DigiTorus86/Teensy-R4ge-Pro/PlatformIO/teensy-r4ge-pro-shooter/include/wav_hihat.h

// Audio data converted from WAV file by wav2sketch

// Converted from hihat.wav, using 44100 Hz, u-law encoding
PROGMEM
const unsigned int wav_hihat[5953] = {
0x01005CB1,0x77766877,0xEAEC2195,0xE0737099,0x82807B70,0x88909012,0x8B822303,0x8C04180B,
0x090B9207,0x878EA413,0x1EB09F15,0x0B9B2122,0xA09E0094,0x51B2B980,0xD1485CCA,0xDACCBF48,
0xE8DFBB47,0xD7B254E2,0xA3E0DED2,0x56D9CDBB,0xBDBAE652,0x33ECEDE7,0xE9F8E450,0xE7C7605C,
0xC7C3C8E3,0x6264BED6,0x2B3ED7C3,0x736C5226,0x51535760,0x29C2DED8,0xD2E3E10D,0xE3E5BAA3,
0x0FC3D2D1,0xE2DFECC3,0x6744E3EE,0xF1E9B453,0x5CE53B58,0x3341465B,0xC03B5A56,0xB60A5293,
0xA4D1DACC,0xCEF0C15F,0xF0E59E5C,0x41C3D5ED,0xE7B56464,0xD2D25CC6,0xB54A5760,0x424C09E1,
0xB7C0D8DA,0xF5F46870,0x53BFCFC6,0x54C9E2CF,0x58BFD95A,0x65656556,0x50ECEA5E,0xD4E8F3D7,
0xD1535FBB,0xE4C937D0,0x626A5F4D,0x57716736,0x4C6B62D6,0x656949E5,0x615AD16B,0x673FF0D6,
0x056054D7,0x91E0E3EA,0xE5B8D4DD,0xD5E6456F,0xD52DCBDA,0x6425EDEE,0x628AC855,0xE487DEDA,
0x54DDD5C3,0xD6DECA48,0x4E23614B,0x5651D7C1,0x9DEBEB41,0xCEE8E4B7,0xE05262C0,0xA4A9D760,
0x34AE5FD0,0xE8BD44DF,0xF559C0F0,0xE5F43FE4,0xDF616357,0x29D1564D,0xC26D66D5,0xD7D6DCDE,
0xD9905433,0xD75E4FD8,0xC5C6D8E4,0x5E68AF42,0x546C18F2,0xE0E1D4D9,0xDBE3C22D,0x719ED751,
0x5561CE45,0x6E4E3C58,0x71755D65,0x66789DDC,0x6E61D5E5,0x68DA616C,0x685CC074,0x70E1CE51,
0x73535E73,0xE6E8E370,0x6FD46463,0x1E62F2C5,0xF4557BC9,0x78E28170,0xD851B867,0x6E656BA1,
0xE27107D4,0x79A85A20,0x70D5F46E,0xBFE4E060,0x645AC550,0xF1E7DC37,0xDC5177AF,0xD0E75465,
0xE05BA422,0x6F6864E2,0xF6F0E1A2,0x416966D7,0xC273D8F5,0x426366E1,0x63CDCF4C,0x54E33B74,
0x65706A54,0x66E0D363,0xF3D55361,0xDDF25920,0xF5266B69,0x44E243C5,0xD96A6362,0x7555E6F6,
0x57EFF7C4,0x54727377,0x661E5A40,0x2EB7C45C,0xE55B5A5D,0xD0CCB2E7,0xD953CAB0,0xE8E0735A,
0xD0637156,0x4829603F,0xC25F5148,0xE67055D7,0x5F5852EC,0xC7AC6D57,0x5859615C,0x4C626340,
0x7D65E342,0x7268446A,0xE01C7377,0x424B620E,0x6D5A3856,0x60E1FBE9,0xEDB5CFB2,0xD83063E2,
0x713CE954,0xDD7A764E,0x71E95E5C,0xF067777F,0x5E7252EC,0x707964E8,0x0D354230,0x68666269,
0x77D0D463,0x604DDF55,0x5ED8E657,0xB5EB5C77,0xF0E8BF3B,0x67685509,0x5E7754E0,0x46F2F2DC,
0x5A6E5C60,0xE35E6C0E,0xC4E16251,0xF7D8625F,0x72DFC0D3,0x67E4F45A,0xC2E0E9D6,0xDFA0616E,
0xCCF5E8C8,0x39665864,0xD3E562B4,0x6A5C4B51,0x5D57F045,0x3B7046E0,0xA22F53D2,0x6D6AEBE5,
0x507754E2,0x6A2B6C56,0x7537C470,0xA4D6707C,0x48E0EB53,0x597B6C25,0xD2936034,0x63B7B7C6,
0x493EA465,0x4F4EE0E0,0xE35851D4,0x5772F1FB,0x61D9F3F1,0xBAF2E462,0xECE3A25D,0xBB40DBE7,
0xCFE53FD2,0xE4D5D589,0xD0E941B7,0xBEECDA61,0xDA606F63,0x43206949,0xF8DD666B,0xD0DB5ADF,
0x6141DE47,0xE8F3E43B,0xE66767E5,0xD36D58C5,0x63A1E3F4,0x57E4E329,0xECD45259,0x3ED7B8C2,
0xB0D9D267,0xF1607463,0xD96169EF,0xC9DDC7B3,0xCB716385,0x5E6EE0F5,0xCE54D5ED,0xD5A15BC1,
0xF3D15755,0xB5DCB0F0,0x67572960,0xC0D6F8E7,0xE0482CD2,0x683548C3,0x6CCBD85C,0xE9EE5B70,
0xE39E665F,0xF1EC5C4C,0xD7DB41C4,0xE9694BE1,0xD9E4CBE7,0x706FD1E7,0xEBF8647A,0x69275766,
0xB531375C,0x7107DEA1,0xB133DB5B,0xF1FAECE7,0x45583842,0xF9F8E1C0,0x52E3625F,0x6662F0D1,
0xF1E3D3E0,0x771CE3D3,0xF4DBB073,0xD64C72E6,0xBC5FE5E3,0xCC48E4F6,0xDAE062B4,0x65E7E756,
0x64E6CC67,0x31F2E475,0x31B1E437,0x92319BE6,0x6B3DDFA1,0x52CB5465,0x449D7279,0x325F6160,
0xCFD96351,0x4A54DCC5,0x6D69D3DB,0xE4EFEDD5,0x6B56E6D1,0x454BEFEB,0xC4D5F2EE,0xD75631BB,
0xF2B75ADC,0xE8587595,0xE35356D7,0xF60561E8,0x26E0EBEB,0xB34FC5AD,0xD6DEEAEB,0xCE695ABD,
0xE0E0C0E2,0xC058735D,0xB9416149,0x5A5448C1,0xF0E26B70,0x195847D0,0x625BDAE8,0xE36963D3,
0x506962D9,0x64666459,0xC2C5DB27,0xE5BE53DA,0xD21EC03A,0x716AECF4,0x66E8E74D,0x6660D263,
0xEBEEFAEA,0xD5CC40D8,0xF4C740D0,0xD6E7B9E8,0xB5C1DF2D,0xD7AEE4EC,0xF1F3DED8,0xCBD0D316,
0x7463DBE5,0x764CEC4D,0xB05E5F68,0x5A65795F,0x6AECEF63,0xCDD2556E,0xDC246F66,0x276FC1EE,
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
};
