DigiTorus86/Teensy-R4ge-Pro/PlatformIO/teensy-r4ge-pro-gravitack/include/explosion_wav.h

// Audio data converted from audio file by wav2sketch_js
// Converted from XPLOSML2.wav, using 11025 Hz, 16 bit u-law encoding

PROGMEM
const unsigned int explosion_wav[3185] = {
0x030031bd,0x00000000,0x23008000,0x746f5b3e,0x6f707172,0x66686a6e,0x5d5f6064,0x97234652,
0xdfd4c8b6,0xebebe7e2,0xeeefefec,0xeceff0ef,0xe5e8eaec,0xd9dde1e3,0xd3d2d3d5,0xd0d0cfd1,
0xd2d0d2d1,0xe0ded9d9,0xe7e4e2e2,0xe5e5e6e5,0xe6e6e7e5,0xe5e7e6e6,0xe9e8e6e7,0xebedece9,
0xeaeaecea,0xe3e4e9eb,0x423623d6,0x32e3ede0,0x66655c5e,0x706e6d6b,0x71717170,0xac185166,
0xe0d8d2c4,0xeae8e6e1,0xebebeceb,0xe9ebebeb,0xe5e7e7e9,0xdce0e1e2,0xc6bac6d3,0xcbcfccd2,
0x983a17c2,0x60585751,0x70666663,0x71706b6f,0x6f6e6c6f,0x73727373,0x74727273,0x72737373,
0x71727273,0x6f707171,0x6064626a,0xc9185b59,0xb1acc8d0,0xd5d1b9ac,0xd3d3d0c4,0xd2d7d7d9,
0xdeddd9d5,0xdadddfdc,0xd8d7d7db,0xcdccd1d3,0xbdc9d1cf,0x1724acb6,0x230023b5,0x4245393a,
0x4a45434b,0x5e5e5f53,0x47484f5b,0x98364845,0xc5c0b6a4,0xd2c6c1c6,0xcccbd2d4,0xd7dad7d1,
0xd4d6dbd9,0xd5d2d1d4,0xd6d4d4d8,0xdbdbdad6,0xd3d8dada,0xd7d8dad5,0xdbdcd8d5,0xe7e1dddc,
0xf1f1ece9,0xf0f1f1f1,0xf3f3f2ef,0xf2f1f2f3,0xf1f1f1f1,0xf3f3f3f3,0xe7f2f3f4,0xebecefe3,
0xd0c7dcea,0xc8dadee0,0xb9c5cec1,0x5f534f44,0x6763615d,0x69696c6c,0x535b5c66,0x2c233a43,
0x2c402c17,0x43393635,0x3a17243d,0x2b41362b,0xc32c3597,0xc4c5c8c1,0x36b6c0c5,0x56544d42,
0x5e5b5b5a,0x595e5f5f,0x5955585a,0x57686961,0x5762624b,0x394d555c,0x80ab8136,0x39ac2432,
0x803e3945,0x554323ab,0x625c6160,0x6f6d6a6a,0x7472716f,0x6c707171,0x68686f70,0x65636467,
0x65616566,0x6b686a6e,0x6f6b676a,0x676a6e6e,0x6a6a6968,0x67656467,0x67676365,0x6c6a6b68,
0x6564646a,0x5a5c5c62,0x535a5f5d,0x50555957,0x412b4445,0x51525151,0x2b363650,0xb60080b5,
0xcdc8bec1,0xacabc5cc,0xc0ba9797,0xc3cbbdac,0xc7d9ddcd,0xc6cdcbcc,0x45483e80,0xe6c71831,
0xe7e9e8e9,0xebe6e3e9,0xece9ebeb,0xf1f0efef,0xf2f2f3f4,0xf3f2f1f0,0xedeeeff0,0xebecebee,
0xefedeeee,0xe7eaeeef,0xe6e7e6e6,0xabcbe1e4,0x5a534198,0x5e5f615f,0x5b606261,0x5f5d5b5b,
0x5a5f6160,0x41424752,0x4e474241,0x31003d52,0x4e4b544d,0xcd31514f,0x3d4744ab,0x40414a4d,
0x353a3932,0x3d504000,0xcbccb297,0xd9d7d4c6,0xdad9deda,0xe5e3dbda,0xb1d7e2e7,0xbdbdac3e,
0xdddbc2b2,0xb2d5d9dc,0xd7d2dccb,0xe1e1d0be,0xb1c9ccdd,0xc0beb5b6,0xdcd5ccbe,0xd8d7d8d6,
0xd6d8ccd3,0x645300c5,0x696b6865,0x72716d6a,0x6f707373,0x70717070,0x6f6e6e6f,0x70747370,
0x69727271,0x525f6463,0x31413d36,0x35363143,0xbab11736,0xe2dad3ce,0xe1e4e6e6,0xe8e6e5e1,
0xe0e7e5e6,0xacc6cfd1,0xb2b5b2b1,0x24312417,0x3118ac97,0x5f438024,0x65625d5f,0x706d6867,
0x72717070,0x71737472,0x73727272,0x616f7171,0x404d5759,0xe3decfb9,0xeae7e6e2,0xe8e7e4e7,
0xebebe5e4,0xeeefedec,0xd7e6ebee,0x24a4b1ac,0x49434032,0x59524d4a,0x54576261,0x98514e5a,
0xc0dbdfe0,0x53422c2b,0x45515759,0xb224353a,0x665b5445,0x63595261,0x52505f65,0x0043393a,
0xc93600ac,0xe9e4e0d4,0xf1f1efee,0xeae9ebf1,0xe2e0e5ea,0xf0eae8e6,0xd1d7d8e7,0xc5c2bac0,
0xcdbdd6d7,0xe9e6e8e4,0xe1e7eceb,0xe4e2e4e3,0xd9e2e7e5,0x2b0023ca,0x455842a3,0x5d53514c,
0x6e686765,0x4150606b,0xc5cac198,0xd6cfd2d0,0xdae0e6e0,0xe8e6e3e1,0xf2f3f2ed,0xeeeff0f1,
0xf1f1ebed,0xe3e9eceb,0x40c2d2dd,0x5b5a5d54,0x5c626263,0x4a47535b,0x41364e45,0x3d3a3949,
0x61615750,0x67676360,0x5b616766,0x4339515a,0x68656256,0x6d6b6a6c,0x6f6e6b6a,0x6767666d,
0x5a63605f,0x67595652,0x696b676a,0x364e656d,0xd9dcd9cb,0xeae3e2dd,0xf1f1eae7,0xf0eff1f3,
0xf4f3edf0,0xf0f0f2f2,0xe5edf1f1,0xcdd3d7dd,0xc8d4d5d2,0x31c2cfcb,0x3e3d4051,0x67635440,
0x665f6466,0x68686768,0x69706867,0x5f5e6465,0x64686259,0x635b5760,0x62646768,0x5861635d,
0x5d4b485a,0x6466635c,0x68636268,0x4d5b6061,0x53594b31,0x463a3239,0xd7dac749,0xedebece2,
0xcbe0e6eb,0xecede9d7,0xecebedef,0xebedf1ee,0xf3f3f2ef,0xebeef0f2,0xf1f3f0ec,0xe1e1e9eb,
0x98d0d3de,0x62616150,0x6b686566,0x6f6d6967,0x6e706e70,0x70706d6c,0xb5445162,0xc4d2cccd,
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
};
