DigiTorus86/Teensy-R4ge-Pro/PlatformIO/teensy-r4ge-pro-gravitack/include/fire_wav.h

// Audio data converted from audio file by wav2sketch_js
// Converted from Fire1.wav, using 11025 Hz, 16 bit u-law encoding

PROGMEM
const unsigned int fire_wav[1185] = {
0x03001270,0x00000000,0x00980000,0x0000ac18,0x181836b2,0x364f4f4f,0xdad1d0d0,0xb6d3cdcb,
0x3a24c3be,0xb6625598,0x364551ac,0x543a6267,0x4d606c41,0x00980055,0x00984b64,0x4fbed4cf,
0xe8e3e1c1,0xdfbedae4,0xdfe8e7f0,0xe2d34bd2,0xc9bae1e2,0xe3cbdc45,0x60514bd5,0x005d65c3,
0x3e636f51,0x2c6d595d,0x55536041,0x6f666324,0x4361586b,0x71635959,0x5c64615d,0x416e6950,
0x24d1cfa4,0xc5ace1d4,0xd8e3e5d0,0xe6e400cf,0xeaf0f4f2,0xdae7e4e5,0xe6d4e1d9,0xe6e6d2a4,
0x2ce0e6ef,0xb2cd455d,0x6951002c,0x45322465,0x3ab26153,0x5c685f65,0x6d5d5443,0x566a6969,
0x5a575247,0x98d49862,0x61566059,0x41ba555f,0xdacddda4,0xb200dae2,0x4fa4c7b6,0xec41664f,
0xe0ebefef,0xbeacd8db,0x4b534fb6,0xcde1eee6,0xe9e0e5da,0x473e43de,0x98b6005a,0xdcd4acba,
0x5c98d1cf,0x5498a449,0xd2595552,0xba3eb2e1,0x6c43a498,0xc14f3a67,0xc94b47c7,0x625551c1,
0x5c003654,0x53604b5a,0xcb3a2400,0x4f5745d5,0x564f5866,0x50acd8c9,0xa4d1dbc3,0xbab22c3a,
0x50505256,0x2cd15064,0x4dc598cd,0x6372624b,0xb6495151,0x324be200,0x655f6f61,0x00d651c5,
0xba36c718,0xd851c132,0xcface0d7,0xb22453d0,0xd4d618e1,0xe2c7e2e1,0xc9e14d00,0xe6ecdfd7,
0xe6b6e9d5,0xd098e3c9,0x47e2cbe0,0x630052d9,0xd3be3ea4,0xf14fd44f,0x5547e251,0x60e658e0,
0x545555e0,0x246d366b,0x58514d69,0x66be6ac3,0xc1735361,0x57433e61,0x49ba60d5,0xd84fb6ac,
0xd1e0b6d0,0xd6b698e1,0xe249f041,0x45f098d3,0xe118d6e6,0x543eba43,0xc936acd5,0x58d56000,
0x415e52c9,0x4f65d573,0x43d34300,0x4d3a9850,0x43d956c1,0x00e0c3c5,0xed66ebc3,0x5cde4763,
0xa4cf57e5,0x00dcac47,0xcf6ad5ba,0x6d005f60,0x515a5849,0x3a6bc961,0x74eb695a,0xd6632c3e,
0x435b435f,0x6350525c,0xdc183eba,0x50e2a436,0xe55dd0e6,0x4fd5d064,0xdacd63e7,0xd1c3ea56,
0x45d7cdd1,0xede0b6f1,0xb2dff055,0xe098d9ed,0xd7d24dc7,0x5de5d332,0xe651ebe0,0xcbddd5e1,
0xd5d436cf,0x4be0cf4f,0xd251d2cb,0x55ba53ac,0x005ae018,0xba475cd0,0x5c36655c,0x603a4d69,
0x5e5d1850,0xa46755c5,0x5e476a5e,0x6b65636f,0x6bb25b68,0x6660dd63,0xe17154e3,0xd2d367be,
0x2cacc94f,0xea4552e3,0x3ae55251,0x6dc3e662,0xb260d0cf,0xd70054d7,0xcfd5d7ac,0xe1bad6e3,
0xd0c9c1d9,0xeb4f00e6,0xf0df61dd,0x36f4005f,0x45c5e855,0x9847d5dc,0xd4ba3ecb,0x18d0ba00,
0x5618d6cb,0x323ac198,0x592cb247,0x6543c54f,0x645ad798,0x325f43c3,0x32b6534d,0x52c9a45c,
0x6251cf51,0x52544f49,0xc1c94b4d,0x55ba9845,0x5f2cd436,0x4f4bb654,0x6455ac45,0x5862544f,
0x006a63ba,0x186c6b18,0x186a6341,0x4b7163da,0xc95d00e1,0x3a5cd1ee,0xc34dc9d9,0xd5e0e0c9,
0xcfeee3d7,0x36e1f0d8,0x56bae1c3,0x6863d8d6,0x6353e000,0x6845e5c5,0xb2e6e400,0xdeece000,
0xe4f3c558,0xe8ead636,0xc1dfc7d4,0xcdb6d2a4,0x5bd4e1c3,0x55e3e5c7,0x52d1de52,0x5a00c95f,
0xd7cb9853,0xd1dab600,0x4500d3e8,0xcb51d8de,0x323ae0c1,0x5acdac00,0xc14b622c,0xb2625f3e,
0x2447c798,0x47c14b58,0xc5496b56,0x5956513a,0x61521818,0x62724d50,0x74646264,0x68596063,
0x5150646c,0x2c592465,0x32d94947,0x5224cfba,0xa4d1c9cb,0x4936d03e,0x4300d600,0x0098b63e,
0x5d3e5c18,0x4bba3653,0xc14b646a,0x554d6366,0x2c607064,0x41455949,0x415745b6,0xbad6c924,
0xd2a4c500,0xd5d1e1e5,0x24dae4d9,0xd8ac453a,0x2ccfdcd8,0xc1d93ec3,0xebd2d041,0xe3d1cfd6,
0xd7d7a4e4,0xdcdddedd,0xe9dfe4e1,0xe1dce6ee,0xe3e3e1db,0xe1ead7e5,0xf4beeae8,0xc5e0e5f0,
0xd8e4e3e8,0x3ac5d1c1,0x5b4bb618,0x2c415964,0x5a59695c,0x4b5b5058,0x5d626152,0x51582c2c,
0x53cb4b50,0x2c59535f,0x56605b49,0x576098b2,0x98c54943,0x54c9dcc7,0xe7ddb25f,0x18b232d7,
0xd800dcd4,0x645258cd,0xd4c1d441,0xd4c94d57,0xb64351df,0x2c476060,0x4b6051b6,0x60410053,
0x5bd2495e,0x3265666c,0x6a6663c1,0x4b41d25c,0x45596963,0x5f36183e,0x4b675149,0x53d3d1ba,
0xe0cb4b56,0xcdba4d32,0x605bd4de,0x5a3ecf47,0x414d6452,0x4f676056,0x6566acba,0xcfcf4300,
0xd7be625c,0x545eb6be,0x4163bae4,0xc9e84d61,0x63684947,0x005955be,0x4dd0364d,0x3e662c55,
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
};
