DigiTorus86/Teensy-R4ge-Pro/PlatformIO/teensy-r4ge-pro-gravitack/include/refuel_wav.h

// Audio data converted from audio file by wav2sketch_js
// Converted from Jump1.wav, using 11025 Hz, 16 bit u-law encoding

PROGMEM
const unsigned int refuel_wav[3553] = {
0x0300376d,0x00000000,0x00000000,0x00000000,0x00000000,0x00000000,0x00000000,0x00000000,
0x00000000,0x00000000,0x00000000,0x00000000,0x00000000,0x18180000,0x24180000,0x2c323224,
0x182c322c,0x32362c24,0x2c2c2c36,0x24001818,0x323a322c,0x36363618,0x41453e3e,0x323a4141,
0x3a3a3232,0x43433a36,0x41364345,0x453a4543,0x434b4143,0x24364747,0x3a323a3e,0x3a435151,
0x49494736,0x41415151,0x00002c32,0x4149413e,0x3243363e,0x24182c00,0x182c3636,0x98323e00,
0x18243200,0x3a3a1818,0x0098ac24,0x24324341,0xc1ac0000,0x2c00acc7,0xd0cfc398,0xb2b2c1c1,
0xcbb200b2,0xc5c9c5cf,0xacc1c3c1,0xc1c1c7b2,0xb6c3b2c1,0xb2000098,0xc3c9c7c5,0xc3acbab2,
0xcdcbc5c1,0xc7c7c1c9,0xc198bacd,0xcdc7bac1,0x00c1cbc7,0xc5c9b200,0x18acbac7,0xa42c003a,
0x36acb6a4,0x32364941,0xc5ba1800,0x323eacac,0x24a42c41,0x98a4412c,0x002c323a,0x00003a32,
0x2c36acb6,0x41414747,0x36413a2c,0x433a4336,0x243a3a45,0x1800a400,0x3a18ac98,0xb6ac2c41,
0x433a2498,0xa4b22c36,0x36a4b22c,0x2c322c3e,0xa432433a,0x324543a4,0xa4a44143,0x189824a4,
0x004b4541,0xc3b6a498,0x410036b2,0xbeba0041,0x182c98be,0x1845433a,0x2cac9800,0x18003618,
0x243a3a24,0xba98a498,0x413a3649,0x00b64136,0x45430032,0xbebe3e41,0x3e000000,0x00494749,
0xb6ba18a4,0x983a3ea4,0xa4ba0024,0x3600a418,0xb2182c24,0xcbb6c5c9,0x98ac24a4,0xc7b224ba,
0x3200c3be,0x0000003a,0xbabe98c7,0xb22c00ac,0xb2b2b6c1,0xbe00c5a4,0xa4beacba,0xaccbc7be,
0xbebabac1,0xcbb6cdc3,0xc3d0c5cf,0x3232ac3a,0x00d3cfc5,0xa449cbcd,0xcdcd47a4,0x4b51982c,
0x32be363e,0x43a4c143,0xc343accf,0x514398ac,0xd24345c5,0x3eba0049,0xd7b22cac,0x49cb98b2,
0x414f184d,0x36005198,0x59492c61,0xac514d32,0x53a44736,0x4345244d,0xc5495600,0x3a2c5358,
0x3641c13a,0xbe434fcd,0x52005449,0x2c4dc724,0xac494fbe,0x3a32364f,0x532cb64b,0x322c4bb2,
0xd13647ac,0x4d243258,0x2c98d4d2,0xc54db6cf,0xcde22c00,0xa400d618,0x98be00cd,0xdb2cd0d5,
0xb2d64ba4,0x32bad445,0xacbe98c9,0xc32cba24,0xd9c124d8,0x003ac724,0xc5d32cd2,0xd0c7c3b6,
0x00c92c36,0xd0becfc1,0x4500be2c,0x18c718ac,0x3298d1c5,0xac3a0051,0x43d498a4,0x432c3e45,
0xd424b62c,0x18ac3a18,0x2c2424b2,0x002c4b32,0xac472c98,0x0041493a,0x4345c9b6,0x51415200,
0x4f45b6ac,0x244f3251,0x5445362c,0x2445412c,0x2441aca4,0x364147a4,0xc932c7c1,0xcbba5b24,
0xbea4c100,0x49cb4341,0x3636c14b,0x184941c1,0xc345c7be,0x98c74dcf,0xbe00984f,0x18d31898,
0xb250b232,0x41240032,0x2c434dd3,0xcb364147,0x00c9514b,0x49004153,0x4b49c92c,0x432cac24,
0x005145c7,0xd1004fc1,0x4f24b656,0x00cb5459,0x4dbab2b2,0x523e4353,0xbe3ed100,0xac5041b2,
0xcda45918,0x00c32ca4,0xc3cb414d,0xc1d8cd32,0x49becb3a,0x36b2cd24,0x3ed2dabe,0xa43ed0cd,
0xdba4acd4,0xd500b6db,0xdac3b2d3,0xe0e000a4,0x18dababa,0x32d2d636,0x3eacd9b2,0xc1b2d3cf,
0xc3c9d2d6,0x00bacdac,0x50c3d1c3,0x0032d1c7,0xc759acd2,0xb24f55c3,0x00c35436,0x3ed10058,
0x5800b655,0x4947d400,0xba574dc1,0xcb2452ba,0x3ed15150,0x4743c147,0x4152524b,0x4b555318,
0x5a43495d,0x5951474f,0xbe593a98,0xb64b622c,0x4b3e554b,0x554b0058,0x002c3632,0x5000433e,
0x6257004d,0xc155beb2,0x003656ba,0x3649a441,0xc9243ecf,0x36c72424,0x00181845,0x98d3a43e,
0x43b2d03e,0xd2d5c9c9,0x00cbe000,0xd1c7c3dc,0x18b6d5c9,0xd6cdc3d9,0xd63ec5c3,0xc5e0acc3,
0xa4c5acbe,0xc7cfcb49,0x5041d1cf,0xd3a4b2cf,0xc7baa4d1,0x00c7b22c,0x45a4cf3a,0xa449bec7,
0xa44d53c1,0x98cd4d41,0x4b00d03a,0x1853acac,0xbe4151cb,0x56325057,0x4549ac55,0xa45041d1,
0x45b24f41,0x324d0043,0xcf4b50c3,0x52ac2c47,0x3e36c52c,0x24ac36b6,0x524b9853,0x001898be,
0x50451898,0xd7a445a4,0x98c9b64d,0x003a00b6,0xbed5d1c7,0xba43b2d0,0xc3c7c9b6,0x980036d0,
0xac32b641,0x47324f00,0xac2cd2ac,0x983ab6b2,0x98c718cf,0xacb2bac7,0x2c49c941,0xaca41898,
0x5400543a,0x0098ac4b,0x3245bac7,0xba45182c,0xac003a32,0x49004324,0x18434118,0xb6494932,
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
};
