DigiTorus86/Teensy-R4ge-Pro/PlatformIO/teensy-r4ge-pro-gravitack/include/warp_wav.h

// Audio data converted from audio file by wav2sketch_js
// Converted from warp1.wav, using 22050 Hz, 16 bit u-law encoding

PROGMEM
const unsigned int warp_wav[5825] = {
0x02005aec,0xa6a6a7a5,0xa8a6a7a7,0xaaaaabab,0xacaaabac,0xadadaeae,0xadadb0af,0xb0b0b0b0,
0xb1b1b2b1,0xb2b2b3b2,0xb2b3b3b3,0xb3b2b3b3,0xb4b4b4b4,0xb5b6b6b6,0xb5b6b8b7,0xb7b7b8b6,
0xb6b7b8b7,0xb9babab8,0xb9b9b9b9,0xb9babab9,0xb9bab9b9,0xbbbbbab9,0xbabababa,0xbbbbb9b9,
0xbabab9b9,0xbabab8b8,0xbbbab9b9,0xbbbab9b9,0xbbbbb9ba,0xbbbbbab9,0xbbbbb9b8,0xbabbb8b8,
0xb9b9b7b7,0xb8b8b6b7,0xb6b6b6b6,0xb5b7b5b5,0xb5b6b5b4,0xb4b6b5b4,0xb3b5b5b3,0xb2b4b3b2,
0xb0b2b2b1,0xb0b1b1b0,0xaeb0afae,0xadb0aeac,0xabadacab,0xabadaaa9,0xa8a9a8a8,0xa8a9a7a7,
0xa7a7a4a5,0xa4a4a2a3,0xa3a3a2a3,0xa0a1a1a1,0x9e9e9a9a,0x93979797,0x90908888,0x8a8e8783,
0x00898783,0x07878403,0x0d80030c,0x150a0a10,0x190c0b15,0x20161619,0x211b1b20,0x221d1b21,
0x231f1d22,0x23201c21,0x24221d21,0x27262223,0x29262123,0x28282527,0x29282525,0x29292424,
0x2a2a2624,0x2b2a2525,0x2c2c2826,0x2b2b2929,0x2b2d2c2b,0x30302c2a,0x30302d2d,0x31312f2e,
0x31313030,0x31302f30,0x31313131,0x31303031,0x322f2f31,0x32313233,0x31303032,0x312e2d31,
0x302d2f31,0x302c2d30,0x2f2b2b30,0x2f2a2a2f,0x2d2a2a2f,0x2d29292b,0x2d29282c,0x2c29292c,
0x2a28262a,0x2825252a,0x26252628,0x25242527,0x20202224,0x1f1f2021,0x1c1b2020,0x1d1c2020,
0x171b2121,0x13131b1b,0x0e111918,0x09091313,0x09081413,0x06051212,0x05041110,0x81800b0b,
0x85880206,0x06070c0d,0x03030f10,0x0a060602,0x02020c10,0x0f0d0702,0x06030309,0x8b898601,
0x86878f8e,0x85858d8d,0x84818a8e,0x80048889,0x8f8a8f8e,0x87888f92,0x8402858b,0x8b01828b,
0x83869091,0x8b818183,0x9188898e,0x8a888d91,0x8e909090,0x888c8c8c,0x8a8a8482,0x9094918a,
0x9c9f958a,0x9c9c9291,0x9ca09c99,0x92999494,0x999d9186,0x85928e8e,0x8b968f03,0x94948308,
0x949a9691,0x8f97948b,0x8596958a,0x90958a08,0x90969183,0x919b9889,0x848f8905,0x8e938706,
0x8e928880,0x8d97948a,0x8f918702,0x999b988f,0x9da09a94,0x99a09e98,0x95999390,0x8e939290,
0x93958d83,0x8287878a,0x868e8800,0x07030303,0x8b86070e,0x85000086,0x86008085,0x83030287,
0x83070189,0x8b00888e,0x88058691,0x0e160c8b,0x15180c00,0x00120f0a,0x89028690,0x860c8192,
0x85088f95,0x84019193,0x0312078e,0x00078f94,0x0c140a85,0x04130a83,0x181c1480,0x131a140e,
0x890f1006,0x0706929a,0x19190588,0x16160909,0x08181814,0x01089091,0x01849595,0x09130c02,
0x100f8790,0x10160803,0x11118383,0x191f1911,0x23231a12,0x151c1c1c,0x191d1109,0x141d1513,
0x03038585,0x82028383,0x11100187,0x1c201911,0x1b1d1715,0x1c1c1715,0x1f1f1a17,0x191d1c1c,
0x8f89820b,0x94949292,0x95939494,0x90919597,0x81858e90,0x1e181105,0x1c1f1f1f,0x030b1217,
0x8e878081,0x04008890,0x01020104,0x0a0f110b,0x1a1d1a11,0x0e141616,0x8e820908,0x99928f8f,
0x9d959599,0xa19c9b9d,0xa7a3a1a1,0xa6a6a6a7,0xa6a5a5a6,0xa4a3a2a4,0x8c969ba1,0x1916160c,
0x191a2020,0x988f0d18,0xa2a29b98,0x9fa19d9d,0x97999797,0x150f0187,0x92920d18,0x10859293,
0x0a0a171a,0x2216120f,0x24252626,0x23252626,0x91910019,0x11018b8b,0x160b0f14,0x181f201e,
0x96968d0d,0x99999696,0x04919999,0x8186050b,0x1a120c0c,0x0102131c,0x12050306,0x211e1f1f,
0x23242726,0x0b111a22,0x9996870b,0xa3a5a099,0x1590989e,0x28232623,0x2223292c,0x928b1421,
0xa0a19990,0x939d9a9a,0x10828288,0x048c0818,0x1d0e1216,0x26232324,0x07142128,0xa3a29785,
0xa9afaaa3,0xa2a6a5a4,0x9ca09e99,0x959e9a94,0x8f9e9a90,0x96958a08,0xa4a39b97,0xaeb1ada6,
0xa8acabaa,0x96a2a3a5,0x21140a87,0x171d2224,0x89810c14,0x91949290,0x98969491,0x04859197,
0x17150d08,0x1f191313,0x121e2021,0x95929183,0xaaa4a29d,0xa3a5aaad,0xa6a3a3a3,0xada9a9a9,
0xadaeb0b0,0x020e95a7,0x9f988f87,0x821380a0,0x9ea1a4a0,0x2b291c91,0x2e2f2b29,0x16272b2b,
0x939ba19a,0x07180d8b,0x211f128c,0x9e07121a,0xa9a5a9aa,0xa0a5abae,0x17251693,0x09899784,
0x80171106,0x1185999a,0x2c332b1b,0x23252224,0x2224201c,0x33322b20,0x27323131,0x8c15181b,
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
};
