DigiTorus86/Teensy-R4ge-Pro/PlatformIO/teensy-r4ge-pro-tombstone/include/explosion_wav.h

// Audio data converted from audio file by wav2sketch_js
// Converted from explode_11k.wav, using 11025 Hz, 16 bit u-law encoding

PROGMEM
const unsigned int explosion_wav[2809] = {
0x03002bc3,0x80008000,0x80008000,0x80008000,0x80008000,0x80008000,0x00000080,0x00800080,
0x00000080,0x00800000,0x80808080,0x00800000,0x00808080,0x01800080,0x01800080,0x01800180,
0x01800281,0x02810182,0x80000000,0x83018000,0x85068404,0x88098609,0x89098909,0x86078908,
0x05818304,0x53545183,0x55535453,0x8a129f48,0x0b850301,0x55511a8c,0x044e5552,0x08880b83,
0x03880689,0x870d8380,0x53545225,0x008d4c55,0x5546a01c,0x32545353,0x8498079b,0x8f828a8e,
0x85988597,0x5255499d,0xa92a5254,0x5439a025,0x44565254,0x988a949c,0x5453554c,0x54545353,
0x01914e56,0x94910f01,0x4e0b818b,0x53555356,0x52545355,0x53535353,0x53535254,0x92315453,
0x06168b03,0x3fa01d87,0x53545355,0x53535353,0x53535352,0x54545453,0x53535454,0x38545353,
0x1fa11f9d,0x56515551,0x1998064c,0x5355459f,0x9b335353,0x83049609,0x99870305,0xa1039991,
0x55515549,0x1ca53153,0x545231aa,0x95465753,0x01909b13,0x96058889,0x8a140982,0x1b961004,
0x535545a1,0x53535454,0x53525353,0x54545453,0x54535453,0x54555454,0x13993454,0x8804808c,
0x56419114,0x53535453,0x54545453,0x54555454,0x53545354,0x05924555,0x89901492,0x16010099,
0x3a9e1a91,0x55535354,0x95209742,0x8f8a0617,0x8080920e,0x818d0c92,0x48a00f83,0x52555356,
0xa724a033,0x53545235,0x82a34656,0x11110c94,0x00948594,0x369d1496,0x55535454,0x8e019543,
0x09998507,0x5453299d,0x54545454,0x40555353,0x169a1da7,0x06861482,0x1b811496,0x53554098,
0x54545455,0x54535354,0x54535454,0x55525453,0x04169344,0x889b9685,0x54522197,0x53535453,
0x42555353,0x18a01ca1,0x5552554e,0x229b1150,0x535440a3,0xa03e5552,0x86908d02,0x31a31388,
0x55525452,0x940da146,0x84818910,0x92118c92,0x54389504,0x43545353,0x1581169c,0x5552554d,
0x1b932350,0x53543ca7,0x54535354,0x54545453,0x54535453,0x54545453,0x53535454,0x189b3e55,
0x5450189b,0x53535453,0x45555353,0x87921199,0x87089203,0x53545223,0x53545455,0x53535353,
0x53545454,0x54545353,0x53535354,0x53545453,0x169f4056,0x87878697,0x53329b15,0x46555355,
0x0a80149f,0x02061112,0x1a848f04,0x53543699,0xa0445453,0x4e0a910e,0x51555355,0x8a84841c,
0x01809184,0x08878186,0x54501112,0x0d4f5552,0x41a41995,0x55545455,0x8f19a23f,0x53555118,
0x54535353,0x94455553,0x8015881d,0x24100c85,0x53535452,0x54535452,0x55535553,0x53535453,
0x1e505453,0x8690070d,0x9f170b0c,0x54535649,0x53535453,0x53535453,0x54545454,0x53545354,
0x52545354,0xa31da525,0x53545436,0x17984455,0x554b8598,0x24525552,0x9096048c,0x900b8986,
0x87000187,0x52554f0a,0x9e0a4f55,0x5540a815,0x3b555353,0x109809a3,0x80840c81,0x8903108b,
0x8c850000,0x554b9711,0x53535353,0x54545453,0x53545454,0x53545354,0x53545354,0x85185154,
0x01100d0c,0x47a00808,0x54545356,0x53555455,0x53545454,0x54535453,0x9b3a5554,0x86049106,
0x8d100c11,0x9d179108,0x54535544,0x1ca23653,0x10880f91,0x11820886,0x0f170d0e,0x18051305,
0x55525550,0x21a2174f,0x545441a4,0x9c3b5553,0x0b0f9205,0x00080310,0xa4148411,0x53535543,
0x07a23854,0x87858d93,0x5439a118,0x54545353,0x54545454,0x88189e32,0x88079217,0x8d048508,
0x5649a113,0x54545553,0x53535453,0x53545453,0x53535454,0x08963a55,0x8d0f0e81,0x5437991c,
0x54545353,0x54545454,0xa21da136,0x5255522b,0x88924956,0x56479c0d,0x32545453,0x00920d9a,
0xa115840d,0x54535541,0x17973f55,0x8e961193,0x04920380,0x429f1280,0x54545255,0x9e22a43a,
0x5255512a,0x8c864b56,0x56479915,0x55545453,0x54545554,0x53545354,0x53545353,0x53545355,
0x9f2f5354,0x53339e22,0x54535454,0x54535354,0x910ca439,0x83850404,0x5455379c,0x53535354,
0x54535453,0x54535453,0x54545453,0x53545353,0x20a24054,0x0b9191a3,0x80030190,0x8f080089,
0x90009610,0x5454564b,0x53545353,0x86904d54,0x5542a008,0x3b545452,0x2794219e,0x55525552,
0x87069d4c,0x110c0e04,0x04818990,0x0f8d1290,0x3f9c1c9a,0x55535355,0x861da53d,0x8a088e02,
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
};
