DigiTorus86/Teensy-R4ge-Pro/PlatformIO/teensy-r4ge-pro-tombstone/include/fire_wav.h

// Audio data converted from audio file by wav2sketch_js
// Converted from fire_11k.wav, using 11025 Hz, 16 bit u-law encoding

PROGMEM
const unsigned int fire_wav[801] = {
0x03000c72,0x81018101,0x81018101,0x00008100,0x01800200,0x04820300,0x05870584,0x0b890401,
0x87820784,0x00908882,0x960c8187,0x55499a14,0x55545453,0x57565656,0x585a5859,0x8312555b,
0x121f8f07,0x529c0712,0x5e605d60,0x921aac36,0x091e1623,0x0d159c87,0x62560927,0x315c615e,
0x46b42db0,0x615e6060,0x1224a750,0x02210413,0x0a13910e,0x61479d24,0x4d616060,0x24a425b3,
0x625e6159,0x2b8d2a5b,0x60614cb2,0x5f5f6061,0x325e605f,0x19a3019e,0x95120688,0x57555844,
0x56555555,0x56565655,0x55565656,0x43575457,0x898e019c,0x9b00918b,0x55565630,0x55565556,
0x56575556,0x55555556,0x56565656,0x57545655,0x810ea349,0x54584c98,0xa22d5357,0x553ba020,
0x44575556,0x168a1d99,0x0e130c13,0x13930e95,0x55573f95,0xa8435755,0x51179917,0x52585558,
0x8e110c11,0x8407840c,0x0d1a8506,0x82230620,0x56389715,0x55555655,0x55565556,0x55565655,
0x56565656,0x57555656,0x9c465856,0x89030123,0x309b1085,0x57575755,0x56545656,0x56565755,
0x57555856,0x15525755,0x900c0715,0x92939092,0x930d8e0c,0x54575327,0x09015057,0x9496910a,
0x93878400,0x95849d08,0xa4128701,0x5655573f,0x1ca34356,0x58512497,0x07525855,0x0f161105,
0x0a19880c,0x9409911a,0x5458531a,0x02165157,0x9601020d,0x50031285,0x55565558,0x57545556,
0x0c189a4f,0x06020a20,0x110a9206,0x552a8607,0x55565656,0x54555556,0x55575556,0x56585658,
0x8b805258,0x83829101,0x500c2384,0x55555559,0x57555656,0x0a91a74e,0x545847a0,0x993d5657,
0x542ca922,0x4b575357,0x8e9791a1,0x9d109d03,0x54575009,0xa2995156,0xa0978896,0x939aa09b,
0x10948493,0x57555652,0x8199914f,0x535544ad,0xa13d5554,0x5215a220,0x54565454,0x55565556,
0x55565454,0x55565656,0x55545654,0xa7465553,0x4c9a8f91,0x55565557,0x54525554,0x21020150,
0x10188a06,0x564e920c,0x54545653,0x57555654,0x57575757,0x54545557,0x55575554,0x91125357,
0x81109a86,0x86131021,0x991c9806,0x16248615,0x57575738,0x55555556,0xa2415755,0x522c9a24,
0x50575357,0x90301d2a,0x55545747,0x2c963e57,0x29032123,0x24221f05,0x2b242a1f,0x0c0b262a,
0x5a565852,0x10131152,0x2a212d1b,0x27151025,0x5425212d,0x545b565a,0x17322238,0x55545746,
0x58575554,0x57595b58,0x57585656,0x55575859,0x57565755,0x272b0a39,0x9a129124,0x901c148c,
0x5b508d25,0x59595a59,0x53575658,0x929a9ba0,0x1c211d8b,0x55584c0c,0x54565657,0x58595656,
0x485b5a5a,0x2aa3049a,0x3020150e,0x93242e28,0x1a0795a5,0x584e2130,0x2c535554,0x988f1fa2,
0xa411aaae,0x56565943,0x2ea04158,0x58522393,0x92505755,0x3fb9a6ab,0x56545457,0x1811a03e,
0x22841309,0x555537a9,0x96465956,0xa5a8b313,0xab80a6a0,0xa396a5a7,0x5a585942,0x5558595a,
0xae295354,0x54358b27,0x55545356,0x50545356,0x53535250,0x57545556,0x54545555,0x57565253,
0x34565654,0x309b27aa,0x54525453,0x56565452,0x89a24457,0xbab9b8b1,0x532eaaaf,0x4f585555,
0x3238332d,0x54555751,0x52545152,0xb5a65056,0xb3b7bdbd,0xa78783a6,0x8b9aa106,0x1e16828a,
0x2520281a,0x525440a6,0x4f505152,0x28515451,0x3aad9008,0x59565655,0xa88e9647,0x595950a7,
0x50555758,0x5452504e,0x43585756,0x8da81493,0x5753554c,0x15192450,0x2a2a311f,0xb1ac8716,
0x342302a7,0x378d3030,0x52535556,0xb9b9c528,0x575850b2,0x57595959,0x5b5b5958,0x5c5c5a5b,
0x54565a5d,0xa79cb4a0,0xacb3a3a9,0x555538b7,0x5657565a,0x5b595655,0x555e5d5d,0x11a32429,
0x0c15848a,0x0c811582,0x57573217,0x56535658,0x5d5b5958,0x5556585b,0xb3b0b113,0x2726168f,
0x880a1730,0x5750202a,0x264d5250,0x41173a12,0x56525556,0x9390b543,0x34323319,0x5957342a,
0x53535557,0xb8b04d52,0x8bb0b0b8,0x18870920,0x2a312c1b,0x58572d18,0x5a5b5a5a,0xb9ba5059,
0xb8b0a3b5,0xa7b6c1bb,0x119dafb3,0x585d4014,0x56555556,0xb6a05459,0xa4b8bbb4,0x29270da0,
0xc1c3b2a1,0x5a5700c1,0x53565757,0x55545453,0x52545456,0x56555353,0x57555858,0x53535357,
0x58585554,0xaaa64e58,0xb7b990aa,0x585722bb,0x5758595a,0x54575759,0x54565354,0xb2b64a54,
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
};
