DigiTorus86/Teensy-R4ge-Pro/PlatformIO/teensy-r4ge-pro-tombstone/include/life_wav.h

// Audio data converted from audio file by wav2sketch_js
// Converted from life_11k.wav, using 11025 Hz, 16 bit u-law encoding

PROGMEM
const unsigned int life_wav[985] = {
0x03000f44,0x00000000,0x00000000,0x00000000,0x80008000,0x80008000,0x00000000,0x00800000,
0x00800080,0x00800080,0x80008000,0x00808000,0x00800080,0x80000080,0x80000000,0x00008000,
0x00000000,0x80000000,0x80008000,0x00800080,0x00800080,0x00008000,0x00800080,0x80800080,
0x80008000,0x00800080,0x00000080,0x80000080,0x00008000,0x00000080,0x80008000,0x80008000,
0x00800000,0x80000080,0x80008000,0x00800000,0x80008000,0x80008000,0x80008000,0x80008000,
0x80008000,0x00800000,0x00800080,0x80000080,0x80008000,0x80008000,0x00008000,0x00800000,
0x80000080,0x80008000,0x80008000,0x00800000,0x80008000,0x00800000,0x80000080,0x80008000,
0x00008000,0x80008000,0x00008000,0x00800080,0x80000080,0x00008000,0x00000080,0x00000080,
0x00800080,0x00800080,0x01800081,0x80010081,0x82008000,0x82028000,0x82028003,0x83808303,
0x00048201,0x81840002,0x0a8a0382,0x18910c88,0x55574d9f,0x8a535556,0xa1199512,0x56545747,
0x071e5555,0x41a01792,0x54565457,0x04903156,0x5737980b,0x57545654,0x82109b3b,0x55562a86,
0x43575456,0x0c9416a2,0x56555415,0xa14a5755,0x9516961a,0x55565652,0x1aa05057,0x4fa11a99,
0x56555556,0x99139652,0x5749a31b,0x54555655,0x17920c14,0x545743a1,0x2a565556,0x9b0f848c,
0x5654573a,0x98385754,0x308f010b,0x54565556,0x17a24157,0x551d0890,0x57545655,0x961aa348,
0x56539012,0x4e575556,0x18981ca2,0x5556509e,0x9a515655,0xa41b9917,0x5654574b,0x10065455,
0x45a21693,0x55565457,0x86852556,0x573ea011,0x57545654,0x03089534,0x54573395,0x3f575456,
0x838e14a0,0x56555523,0xa2465754,0x010f9418,0x55565553,0x1aa34c57,0x519a1798,0x56555556,
0x99189c51,0x574da31a,0x53565655,0x18961387,0x545747a3,0x20555556,0xa1148f02,0x56545741,
0x90315654,0x36980900,0x54565457,0x119b3c57,0x56288b84,0x57545654,0x9219a144,0x5554110c,
0x4a575556,0x16961da3,0x55565296,0xa0505655,0xa11b981d,0x5655574f,0x17935256,0x49a21b97,
0x55565457,0x900d1854,0x5743a116,0x56555654,0x1082882d,0x54573a9a,0x39575457,0x90000a95,
0x5655562d,0xa1425854,0x19098e16,0x54565555,0x1ba24857,0x53901593,0x57555556,0x951ca14e,
0x5650a01b,0x52565555,0x1d951695,0x55574aa4,0x12545556,0xa31a900c,0x56545744,0x8b285655,
0x3c9d0f86,0x54565457,0x02993757,0x56319501,0x57545655,0x8a11a040,0x55552185,0x47575456,
0x118514a3,0x5555538a,0xa34d5754,0x9e169520,0x55555651,0x1b9f5156,0x4ca61898,0x55565457,
0x92100253,0x5746a313,0x55555554,0x15870522,0x545740a3,0x32565456,0x99020991,0x56545636,
0x993d5754,0x26888611,0x54565455,0x1ea24557,0x5402179b,0x57545654,0x9c1ea34a,0x55539918,
0x42575456,0x9e0e849c,0x5555573b,0x85165456,0x509f138b,0x57545656,0x820f9f47,0x55563292,
0x25555556,0xa2178b8f,0x5555574c,0x12a24c57,0x5526858f,0x56555655,0x05859131,0x555748a1,
0x9b4f5755,0x1d878a12,0x55565554,0x00953757,0x5744a00c,0x51565655,0x0c8f1293,0x56555301,
0x9b405755,0x409e090e,0x56565557,0x910c8553,0x56528f11,0x43575556,0x968512a0,0x5655573a,
0x06175455,0x509a0f8c,0x57555556,0x8716a147,0x55563397,0x26555556,0xa1118582,0x5555574d,
0x17a14b57,0x56298d84,0x56555655,0x12039131,0x555749a1,0x9d4f5655,0x1d008915,0x55565554,
0x03973857,0x5744a110,0x51565555,0x078d1293,0x56565305,0x9d3f5755,0x40a00c0b,0x56565557,
0x890f0253,0x56519410,0x44575555,0x9904139f,0x56555639,0x031c5455,0x509d1289,0x57555556,
0x020fa247,0x55563394,0x25555556,0xa1168b85,0x5555574d,0x16a14b57,0x55298883,0x56555655,
0x17018f31,0x555748a0,0x9d4f5655,0x1e058413,0x54565554,0x04943857,0x5644a015,0x51565555,
0x06891695,0x56555380,0xa13e5755,0x409e8509,0x55565558,0x8d8d8953,0x56528d08,0x43565555,
0x848f1aa8,0x55545738,0x93245355,0x5640a414,0x40575455,0x219a19a2,0x57545653,0x1488984e,
0x545848a0,0xa52f5456,0x5637a423,0x44565455,0x188e1aa6,0x57545751,0x1a8b814f,0x545746a1,
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
};
