DigiTorus86/Teensy-R4ge-Pro/PlatformIO/teensy-r4ge-pro-tombstone/include/theme_wav.h

// Audio data converted from audio file by wav2sketch_js
// Converted from theme_11k.wav, using 11025 Hz, 16 bit u-law encoding

PROGMEM
const unsigned int theme_wav[12145] = {
0x0300bdaa,0x80008000,0x80008000,0x00008000,0x00800080,0x80008000,0x80000000,0x00008000,
0x00800080,0x00800080,0x80008000,0x80008000,0x80008000,0x80008000,0x80008000,0x00800000,
0x00800080,0x00800080,0x00800080,0x00000080,0x00800080,0x80008000,0x00008000,0x00800080,
0x00800080,0x80000080,0x80008000,0x80008000,0x00000000,0x80008000,0x80008000,0x00808000,
0x00800080,0x00800080,0x00000000,0x00000080,0x00800080,0x00800080,0x80000080,0x00800000,
0x80000000,0x00008000,0x00000000,0x00800000,0x00008080,0x80000000,0x00000000,0x00000000,
0x80808000,0x00800080,0x00800080,0x80008000,0x00008000,0x00000000,0x00800080,0x00800080,
0x00800080,0x80800080,0x00800080,0x00800081,0x00008080,0x81000080,0x80808181,0x82008080,
0x82028400,0x84000081,0x09038585,0x81038380,0x03830406,0x04880b04,0x048b078b,0x08870f81,
0x37991589,0x55565455,0x55555555,0x4a575456,0x0d9214a2,0x11821581,0x47a11992,0x54555357,
0x54555455,0x38565455,0x0983189a,0x808e0f85,0x52118005,0x54555455,0x54555554,0x02525554,
0x8e838b81,0x04090207,0x56389820,0x55545554,0x55545554,0xa2485653,0x9408911b,0x8b0f8b12,
0x56499f1a,0x55545653,0x55545554,0x94365554,0x050f8215,0x05848b0f,0x55520b07,0x54545554,
0x54555555,0x10005255,0x06800700,0x1491108b,0x54563a9e,0x54555455,0x54555455,0x13a44656,
0x10900f96,0x198f1492,0x53564ba0,0x54555455,0x54555455,0x11923255,0x82841187,0x84000403,
0x5455531d,0x55555554,0x56545554,0x85118a51,0x8b028b0e,0xa0179114,0x5553563d,0x55545554,
0x56535554,0x9417a244,0x91059113,0x9d17930f,0x5554564c,0x55545554,0x55545554,0x890a9230,
0x85808509,0x218b0580,0x54555453,0x54555454,0x50565455,0x0e8d1292,0x0f890f8e,0x40a11990,
0x54555356,0x54555455,0x43565455,0x139418a1,0x10910f87,0x4e9a158c,0x54555456,0x54555455,
0x28555455,0x098a0892,0x87858304,0x54268b08,0x54545554,0x55545554,0x994f5654,0x8c0f9014,
0x930a920e,0x5641a219,0x55545554,0x55545554,0xa1425653,0x91109317,0x900f8b11,0x564f9914,
0x55545554,0x55545554,0x91245454,0x05048006,0x0e810403,0x54552a8f,0x54555455,0x54555455,
0x149e4e56,0x15881093,0x16911084,0x535643a1,0x54555455,0x53555455,0x16a04056,0x11901296,
0x168e0f85,0x54565092,0x54555455,0x54545455,0x82881f54,0x06060284,0x940f860c,0x5554552f,
0x55545554,0x56545554,0x941b9e4d,0x8f0e9310,0xa2189510,0x56535644,0x55545554,0x56535554,
0x90189e3e,0x85118f0b,0x93118d0b,0x55545551,0x54545554,0x53555454,0x0a00021c,0x0b800780,
0x31981088,0x54555455,0x54555455,0x4b565455,0x1798199d,0x1291108d,0x46a11794,0x53555456,
0x54555455,0x3b565455,0x148a1499,0x0e860c86,0x518d0a8d,0x54545455,0x54545454,0x16525555,
0x830d8f02,0x8b098a0b,0x5535990c,0x55545554,0x55545554,0xa04a5654,0x8e159317,0x92118e11,
0x5647a21a,0x55545553,0x55545554,0x9a385654,0x82118c15,0x850a8605,0x55520806,0x54545554,
0x54555454,0x03085255,0x0f850d00,0x128b018c,0x5456399b,0x54555455,0x53555455,0x18a14856,
0x128f1291,0x198e128b,0x54564aa0,0x54555455,0x54555455,0x109a3555,0x0b850889,0x03810603,
0x54555315,0x54545554,0x55545554,0x88058751,0x880e8610,0x9c168d0d,0x5554563b,0x55545554,
0x56535554,0x9113a345,0x8d148b13,0x9f1a9110,0x5554564b,0x55545554,0x55545554,0x860d9a31,
0x80068709,0x1c870102,0x54545553,0x54545455,0x50555455,0x0d880f90,0x11890f8d,0x3ea0178f,
0x54555456,0x54555455,0x44565355,0x138f17a1,0x0e89128f,0x4d9d1691,0x54555456,0x54555455,
0x2e555455,0x03830695,0x80810885,0x54228d04,0x55545555,0x55545554,0x90505654,0x92108d12,
0x910d920a,0x5640a017,0x55545553,0x55545554,0xa2435653,0x930f9217,0x920f9209,0x564e9b13,
0x55545554,0x55545554,0x8f295454,0x85008509,0x07838081,0x5454258d,0x54555455,0x54555455,
0x16984f56,0x08930f8e,0x18950f92,0x535642a1,0x54555455,0x53555455,0x18a24156,0x0a921191,
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
};
