DigiTorus86/Teensy-R4ge-Pro/PlatformIO/teensy-r4ge-pro-gravitack/include/tick_wav.h

// Audio data converted from audio file by wav2sketch_js
// Converted from plip1.wav, using 22050 Hz, 16 bit u-law encoding

PROGMEM
const unsigned int tick_wav[577] = {
0x020008ee,0x0e0d0f0d,0x0d0e0d0e,0x0c0d0f0d,0x0e0c0d0d,0x0c0d0d0e,0x0e0c0d0d,0x0c0b0d0c,
0x0d0c0b0c,0x0d0f0f0d,0x0e0c0d0d,0x0c0c0b0c,0x0c0f0e0a,0x90010a0a,0x089ea29d,0x7f7a6540,
0x9a747f7f,0xfffffef4,0x74a2f7ff,0x7a7f7f7f,0xfffbe562,0xe3faffff,0x7f7f7b67,0xf5c9717e,
0xfdfffffe,0x7e7655ee,0x56767f7f,0xfffffaea,0x6dcbf4fe,0x7a7f7f7b,0xfdf5d668,0xe4f9ffff,
0x7f7e775f,0xeb43727d,0xfbfffefa,0x7b7023ee,0x61767e7f,0xfefcf5dd,0x64d7f3fd,0x797e7d77,
0xf9edab6d,0xe6f7fdfd,0x7d7b714d,0xe058727b,0xf9fdfbf4,0x7666c4ef,0x66767c7c,0xfcf7edc1,
0x56dff3fa,0x787c7a71,0xf3e24e6f,0xe9f5faf9,0x7a756991,0xca627379,0xf7f9f6ed,0x715ad5f0,
0x6a757978,0xf7f2e240,0x39e3f2f7,0x76787469,0xecd15b70,0xeaf4f6f4,0x76705eca,0x28657277,
0xf4f5f1e2,0x6846ddef,0x6c747673,0xf2ead354,0xc0e6f1f4,0x74746f60,0xe29b6170,0xebf2f3f0,
0x71684cd7,0x4f687174,0xf2f1e9d4,0x60a9e2ee,0x6c72726d,0xede2b35d,0xd2e7f0f1,0x7270664e,
0xd446646f,0xebf0efe7,0x6b5e93df,0x59697070,0xefebe1b8,0x4dcfe4ed,0x6c706d65,0xe5d44362,
0xdbe8edec,0x6e685c82,0xb556666d,0xeaece8df,0x624bcce2,0x60696d6a,0xe9e3d142,0xa1d9e6ea,
0x6a6b6557,0xdaa85565,0xe1e8e9e5,0x675f43ce,0x4760676a,0xe8e6e0c8,0x50b9dbe5,0x64686762,
0xe2d22e58,0xd4e2e6e6,0x6763561c,0xac516166,0xe5e6e2d6,0x5938cddf,0x5e646663,0xe2d8bb4b,
0xc8dce3e5,0x6562593f,0xb9495c63,0xe2e4e1d7,0x5636c9db,0x5d636461,0xdfd2a54e,0xd1dde2e3,
0x625c4f97,0x39556063,0xe2e0d7c4,0x30c7d8e0,0x61615d52,0xc435535d,0xe0e1dfd6,0x4b8accd9,
0x5f616058,0xcb8b4958,0xdee0ded8,0x46a2ccd8,0x60605d55,0xb140525b,0xdfddd7ce,0xbcd0d8de,
0x5c564d32,0x545a5e5f,0xd0c02347,0xdddedcd7,0xb7cbd5da,0x5852472b,0x5a5d5d5c,0x9f3c4d55,
0xdad6d0c3,0xd6dadcdc,0x3d96c2d0,0x5b59544d,0x51575a5c,0xc8b42c45,0xdbdad7d2,0xcad3d7da,
0x504322b8,0x5a5b5955,0x404e5458,0xd3cbbc14,0xd9dad9d7,0xb1c6d1d5,0x5550452f,0x57595a58,
0x8c3c4a52,0xd6d3ccbf,0xd4d7d9d9,0x31aac3cf,0x57555045,0x51555859,0xbf953948,0xd8d6d2cb,
0xcdd3d6d8,0x4532a7c2,0x58565450,0x47515457,0xcabe9537,0xd7d7d5d1,0xc1ccd2d5,0x4e4430a7,
0x56575553,0x38475054,0xd0c8bb8d,0xd4d6d6d4,0xa9c1ccd2,0x524c422d,0x53555654,0x04394750,
0xd3cfc6b8,0xd1d4d5d4,0x29acc2cb,0x54514a41,0x4f535455,0xb5133a47,0xd3d1cdc4,0xcbd1d3d4,
0x3f24afc1,0x54525049,0x474f5254,0xc3b2193b,0xd3d2d0cb,0xc1cad0d2,0x473d21b0,0x5353524f,
0x3b464e52,0xc9c1b01e,0xd1d2d2d0,0xafc1c9cf,0x4d463b20,0x51525251,0x1e3a464d,0xcec8c0af,
0xced1d1d1,0x20adc0c8,0x504c463b,0x4c505152,0xb01a3944,0xd0cdc8c0,0xc6ccd0d1,0x3b23a8bd,
0x51504c45,0x434a4f51,0xc1b11036,0xd0cfcdc7,0xb9c4cace,0x463d29a1,0x50504f4c,0x3140474d,
0xc8c1b48e,0xcccececc,0x8eb4c1c8,0x4c474031,0x4a4e504f,0xa0283c45,0xccc8c3b8,0xc5c9cccd,
0x3619abbd,0x4e4c4842,0x41474c4e,0xbdad1535,0xcccbc9c4,0xb5c1c6ca,0x443c2b98,0x4c4d4c49,
0x2a3b4449,0xc6c1b59a,0xc7cacbc9,0x1ca7bac3,0x4a474136,0x45494c4c,0xaf08313f,0xc9c7c3bc,
0xbcc3c7c9,0x3e3105af,0x4b4b4844,0x34404549,0xc2b9a719,0xc7c8c8c6,0x89b0bdc3,0x47433c2d,
0x45484a49,0xa41c3540,0xc7c4c0b7,0xbcc2c6c7,0x3a2b8cb0,0x49484642,0x333f4447,0xc0b6a41b,
0xc5c6c6c4,0x00adbac1,0x46423b2e,0x43464848,0xa811313c,0xc5c3c0b7,0xb6c0c3c5,0x3c3115a5,
0x46474642,0x29384144,0xc0b9ae8b,0xc1c4c4c3,0x2498b1bb,0x45433f35,0x3c424546,0xb3a11c32,
0xc3c3c1bc,0xa6b5bec2,0x413a2f11,0x43454544,0x8f26363f,0xc2bfb8ad,0xb7bfc2c2,0x36278bac,
0x4444423e,0x2c384043,0xbdb5a708,0xbfc1c2c1,0x2294afb8,0x43413c33,0x383f4243,0xb3a4102d,
0xc0c1c0bb,0x94adb7be,0x403b3322,0x3e424342,0xa40f2c37,0xc0bfbab3,0xabb5bcc0,0x3b332390,
0x40424240,0x0227343c,0xbebab3a6,0xb3babebf,0x342803a5,0x4141403c,0x2031393f,0xbab5ab93,
0xb6bbbebd,0x2e189caf,0x40403d37,0x2a353b40,0xb7b0a10f,0xb8bbbdbb,0x2580a5b2,0x403e3933,
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
};
