DigiTorus86/Teensy-R4ge-Pro/PlatformIO/teensy-r4ge-pro-gravitack/include/Levels.h

#define MAX_LEVEL 6

const int Level_01[107] = {
  // ground segments (32)
  0,  120,
  40, 160,
  80, 160,
  100,180,
  180,180,
  200,160,
  240,120,
  260,140,
  280,140,
  320,100,
  999,999,
  999,999,
  999,999,
  999,999,
  999,999,
  999,999,
  999,999,
  999,999,
  999,999,
  999,999,
  999,999,
  999,999,
  999,999,
  999,999,
  999,999,
  999,999,
  999,999,
  999,999,
  999,999,
  999,999,
  999,999,
  999,999,
  
  // fuel (8)
  50, 144,
  266,124,
  999,999,
  999,999,
  999,999,
  999,999,
  999,999,
  999,999,
  
  // turrets (8)
  120,170, 1, 
  999,999, 1,
  999,999, 1,
  999,999, 1,
  999,999, 1,
  999,999, 1,
  999,999, 1,
  999,999, 1,

  // player start pos
  160, 40,
  // level delay
  30
};

const int Level_02[107] = {
  // ground segments (32)
  0,  220,
  40, 180,
  80, 180,
  100,160,
  100,120,
  120,100,
  140,100,
  180, 60,
  200, 80,
  220, 80,
  260,120,
  280,120,
  320,160,
  999,999,
  999,999,
  999,999,
  999,999,
  999,999,
  999,999,
  999,999,
  999,999,
  999,999,
  999,999,
  999,999,
  999,999,
  999,999,
  999,999,
  999,999,
  999,999,
  999,999,
  999,999,
  999,999,
  
  // fuel (8)
  70, 164,
  210, 64,
  999,999,
  999,999,
  999,999,
  999,999,
  999,999,
  999,999,
  
  // turrets (8)
  120, 90, 1,
  260,110, 1,
  999,999, 1,
  999,999, 1,
  999,999, 1,
  999,999, 1,
  999,999, 1,
  999,999, 1,

  // player start pos
  20, 40,
  // level delay
  25
};

const int Level_03[107] = {
  // ground segments (32)
  0,  60,
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
  // fuel (8)
   40,104,
  252,104,
  190,204,
  200, 44,
  999,999,
  999,999,
  999,999,
  999,999,
  
  // turrets (8)
   50,210, 1,
  170, 80, 3,
  290,160, 3,
  999,999, 1,
  999,999, 1,
  999,999, 1,
  999,999, 1,
  999,999, 1,

  // player start pos
   90, 40,
  // level delay
    10
  
};
