DigiTorus86/Teensy-R4ge-Pro/ArduinoIDE/teensy-r4ge-pro-test/icons.h

/* Image include file for RGB565 bitmap 
 * Original filename: brightness16.png
 * Width: 16 * Height: 16
 */

const PROGMEM uint16_t brightness_icon[256] = {
0x000000, 0x000000, 0x000000, 0x000000, 0x000000, 0x000000, 0x000000, 0x000000, // 8 pixels
0x000000, 0x000000, 0x000000, 0x000000, 0x000000, 0x000000, 0x000000, 0x000000, // 16 pixels
0x000000, 0x000000, 0x000000, 0x000000, 0x000000, 0x000000, 0x000000, 0x00F7E0, // 24 pixels
0x000000, 0x000000, 0x000000, 0x000000, 0x000000, 0x000000, 0x000000, 0x000000, // 32 pixels
0x000000, 0x000000, 0x000000, 0x000000, 0x00F7E0, 0x000000, 0x000000, 0x000000, // 40 pixels
0x000000, 0x000000, 0x00F7E0, 0x000000, 0x000000, 0x000000, 0x000000, 0x000000, // 48 pixels
0x000000, 0x000000, 0x000000, 0x000000, 0x000000, 0x000000, 0x000000, 0x000000, // 56 pixels
0x000000, 0x000000, 0x000000, 0x000000, 0x000000, 0x000000, 0x000000, 0x000000, // 64 pixels
0x000000, 0x00F7E0, 0x000000, 0x000000, 0x0052C3, 0x00C622, 0x00E760, 0x00F8E0, // 72 pixels
0x00E760, 0x00C622, 0x0052C3, 0x000000, 0x000000, 0x00F7E0, 0x000000, 0x000000, // 80 pixels
0x000000, 0x000000, 0x000000, 0x008423, 0x00F880, 0x00F7E0, 0x00F7E0, 0x00F7E0, // 88 pixels
0x00F7E0, 0x00F7E0, 0x00F880, 0x008423, 0x000000, 0x000000, 0x000000, 0x000000, // 96 pixels
0x000000, 0x000000, 0x0031A3, 0x00E760, 0x00F7E0, 0x00F7E0, 0x00F7E0, 0x00F7E0, // 104 pixels
0x00F7E0, 0x00F7E0, 0x00F7E0, 0x00E760, 0x0031A3, 0x000000, 0x000000, 0x000000, // 112 pixels
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
0x0022B0, 0x0022B0, 0x0022B0, 0x0022B0, 0x0022B0, 0x000000, 0x000000, 0x000000, // 416 pixels
0x000000, 0x000000, 0x000000, 0x000000, 0x000000, 0x000000, 0x000000, 0x000000, // 424 pixels
0x000000, 0x000000, 0x000000, 0x000000, 0x000000, 0x000000, 0x000000, 0x000000, // 432 pixels
};
